staskevich/MIDICPU/src/pinconfigs.asm

; MIDI CPU
; copyright John Staskevich, 2017
; john@codeandcopper.com
;
; This work is licensed under a Creative Commons Attribution 4.0 International License.
; http://creativecommons.org/licenses/by/4.0/
;
; pinconfigs.asm
;
; Default pin configurations.
;
		list		p=16f887
   		#include	<p16f887.inc>
   		#include	<mc.inc>

pinconfigs	code	0x1C00

; ======================
; Config Layer 0
; ======================
; Pin configs 0-23
; Pin 0
		data	0x0044
		data	0x0000
		data	0x003C
		data	0x007F
; Pin 1
		data	0x0044
		data	0x0000
		data	0x003D
		data	0x007F
; Pin 2
		data	0x0044
		data	0x0000
		data	0x003E
		data	0x007F
; Pin 3
		data	0x0044
		data	0x0000
		data	0x003F
		data	0x007F
; Pin 4
		data	0x0044
		data	0x0000
		data	0x0040
		data	0x007F
; Pin 5
		data	0x0044
		data	0x0000
		data	0x0041
		data	0x007F
; Pin 6
		data	0x0044
		data	0x0000
		data	0x0042
		data	0x007F
; Pin 7
		data	0x0044
		data	0x0000
		data	0x0043
		data	0x007F
; Pin 8
		data	0x0044
		data	0x0000
		data	0x0044
		data	0x007F
; Pin 9
		data	0x0044
		data	0x0000
		data	0x0045
		data	0x007F
; Pin 10
		data	0x0044
		data	0x0000
		data	0x0046
		data	0x007F
; Pin 11
		data	0x0044
		data	0x0000
		data	0x0047
		data	0x007F
; Pin 12
		data	0x0044
		data	0x0000
		data	0x0048
		data	0x007F
; Pin 13
		data	0x0044
		data	0x0000
		data	0x0049
		data	0x007F
; Pin 14
		data	0x0044
		data	0x0000
		data	0x004A
		data	0x007F
; Pin 15
		data	0x0044
		data	0x0000
		data	0x004B
		data	0x007F
; Pin 16
		data	0x0044
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

		data	0x007F
		data	0x0000
		data	0x0000
		data	0x0000

		data	0x007F
		data	0x0000
		data	0x0000
		data	0x0000

		data	0x007F
		data	0x0000
		data	0x0000
		data	0x0000

		data	0x007F
		data	0x0000
		data	0x0000
		data	0x0000

		data	0x007F
		data	0x0000
		data	0x0000
		data	0x0000

		end
