staskevich/MIDICPU/src/eeprom.asm

; MIDI CPU
; copyright John Staskevich, 2017
; john@codeandcopper.com
;
; This work is licensed under a Creative Commons Attribution 4.0 International License.
; http://creativecommons.org/licenses/by/4.0/
;
; eeprom.asm
;
; Default values stored in EEPROM.
;
		list		p=16f887
		#include	<p16f887.inc>

; ==================================================================
; ==================================================================
; ==================================================================
;
; DATA EEPROM FILL
;
; ==================================================================
; ==================================================================
; ==================================================================

eedata	code	0x2100

; firmware version
		data	0x04
; checksum
		data	0xB6
		data	0x07
; analog threshold
		data	0x06
; analog smoothing
		data	0x04
; VREF
		data	0x00
; Default Note Velocity
		data	0x7F
; Default CC "On" Value
		data	0x7F
; Default CC "Off" Value
		data	0x00
; Active Sense
		data	0x00
; Encoder Initial Values (12)
		data	0x00
		data	0x00
		data	0x00
		data	0x00
		data	0x00
		data	0x00
		data	0x00
		data	0x00
		data	0x00
		data	0x00
		data	0x00
		data	0x00
; Select Datamasks (15)
		data	B'00000000'
		data	B'00000001'
		data	B'00000011'
		data	B'00000111'
		data	B'00001111'
		data	B'00011111'
		data	B'00111111'
		data	B'01111111'
		data	B'10000000'
		data	B'11000000'
		data	B'11100000'
		data	B'11110000'
		data	B'11111000'
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
		data	0x68
		data	0x69
		data	0x6A
		data	0x6B
		data	0x6C
		data	0x6D
		data	0x6E
		data	0x6F
		data	0x70
		data	0x71
		data	0x72
		data	0x73
		data	0x74
		data	0x75
		data	0x76
		data	0x77
		data	0x78
		data	0x79
		data	0x7A
		data	0x7B
		data	0x7C
		data	0x7D
		data	0x7E
		data	0x7F

		end
