staskevich/MIDICPU/src/sysexbuffer.asm

; MIDI CPU
; copyright John Staskevich, 2017
; john@codeandcopper.com
;
; This work is licensed under a Creative Commons Attribution 4.0 International License.
; http://creativecommons.org/licenses/by/4.0/
;
; sysexbuffer.asm
;
; Default contents of sysex uffer used for generating outbound SysEx.
;
		list		p=16f887
   		#include	<p16f887.inc>

; Outbound SysEx Data Buffer
sysexbuffer	code	0x1F00
;		org		0x1F00

		data 0x0000
		data 0x0001
		data 0x0002
		data 0x0003
		data 0x0004
		data 0x0005
		data 0x0006
		data 0x0007
		data 0x0008
		data 0x0009
		data 0x000A
		data 0x000B
		data 0x000C
		data 0x000D
		data 0x000E
		data 0x000F
		data 0x0010
		data 0x0011
		data 0x0012
		data 0x0013
		data 0x0014
		data 0x0015
		data 0x0016
		data 0x0017
		data 0x0018
		data 0x0019
		data 0x001A
		data 0x001B
		data 0x001C
		data 0x001D
		data 0x001E
		data 0x001F
		data 0x0020
		data 0x0021
		data 0x0022
		data 0x0023
		data 0x0024
		data 0x0025
		data 0x0026
		data 0x0027
		data 0x0028
		data 0x0029
		data 0x002A
		data 0x002B
		data 0x002C
		data 0x002D
		data 0x002E
		data 0x002F
		data 0x0030
		data 0x0031
		data 0x0032
		data 0x0033
		data 0x0034
		data 0x0035
		data 0x0036
		data 0x0037
		data 0x0038
		data 0x0039
		data 0x003A
		data 0x003B
		data 0x003C
		data 0x003D
		data 0x003E
		data 0x003F
		data 0x0040
		data 0x0041
		data 0x0042
		data 0x0043
		data 0x0044
		data 0x0045
		data 0x0046
		data 0x0047
		data 0x0048
		data 0x0049
		data 0x004A
		data 0x004B
		data 0x004C
		data 0x004D
		data 0x004E
		data 0x004F
		data 0x0050
		data 0x0051
		data 0x0052
		data 0x0053
		data 0x0054
		data 0x0055
		data 0x0056
		data 0x0057
		data 0x0058
		data 0x0059
		data 0x005A
		data 0x005B
		data 0x005C
		data 0x005D
		data 0x005E
		data 0x005F
		data 0x0060
		data 0x0061
		data 0x0062
		data 0x0063
		data 0x0064
		data 0x0065
		data 0x0066
		data 0x0067
		data 0x0068
		data 0x0069
		data 0x006A
		data 0x006B
		data 0x006C
		data 0x006D
		data 0x006E
		data 0x006F
		data 0x0070
		data 0x0071
		data 0x0072
		data 0x0073
		data 0x0074
		data 0x0075
		data 0x0076
		data 0x0077
		data 0x0078
		data 0x0079
		data 0x007A
		data 0x007B
		data 0x007C
		data 0x007D
		data 0x007E
		data 0x007F

		end
